martinclausen2/Lichtobjekt/Inc/main.h

#define ENC_SW_Pin GPIO_PIN_0
#define ENC_SW_GPIO_Port GPIOA
#define ENC_SW_EXTI_IRQn EXTI0_IRQn
#define LED_2_PWM_Pin GPIO_PIN_1
#define LED_2_PWM_GPIO_Port GPIOA
#define IR_IN_Pin GPIO_PIN_2
#define IR_IN_GPIO_Port GPIOA
#define U_Bat_Pin GPIO_PIN_3
#define U_Bat_GPIO_Port GPIOA
#define U_Pwr_Pin GPIO_PIN_4
#define U_Pwr_GPIO_Port GPIOA
#define LED_1_PWM_Pin GPIO_PIN_5
#define LED_1_PWM_GPIO_Port GPIOA
#define STATUS_LED_R_PWM_Pin GPIO_PIN_6
#define STATUS_LED_R_PWM_GPIO_Port GPIOA
#define STATUS_LED_G_PWM_Pin GPIO_PIN_7
#define STATUS_LED_G_PWM_GPIO_Port GPIOA
#define STATUS_LED_B_PWM_Pin GPIO_PIN_0
#define STATUS_LED_B_PWM_GPIO_Port GPIOB
#define PERIP_PWR_Pin GPIO_PIN_2
#define PERIP_PWR_GPIO_Port GPIOB
#define IR_OUT_Pin GPIO_PIN_12
#define IR_OUT_GPIO_Port GPIOB
#define BRIGHT_IN_Pin GPIO_PIN_14
#define BRIGHT_IN_GPIO_Port GPIOB
#define J_LinkRX_Pin GPIO_PIN_9
#define J_LinkRX_GPIO_Port GPIOA
#define J_LinkTX_Pin GPIO_PIN_10
#define J_LinkTX_GPIO_Port GPIOA
#define SWDIO_Pin GPIO_PIN_13
#define SWDIO_GPIO_Port GPIOA
#define SWCLK_Pin GPIO_PIN_14
#define SWCLK_GPIO_Port GPIOA
#define BRIGHT_LOW_Pin GPIO_PIN_15
#define BRIGHT_LOW_GPIO_Port GPIOA
#define BRIGHT_HIGH_Pin GPIO_PIN_3
#define BRIGHT_HIGH_GPIO_Port GPIOB
#define Charging_Status_Pin GPIO_PIN_4
#define Charging_Status_GPIO_Port GPIOB
#define ENC_B_Pin GPIO_PIN_6
#define ENC_B_GPIO_Port GPIOB
#define ENC_A_Pin GPIO_PIN_7
#define ENC_A_GPIO_Port GPIOB
